mateoherrera-dev/paleta-pingpong/herramientas/segmentar.py

"""Segmenta los archivos crudos en ventanas individuales para Edge Impulse.

Uso:
    python herramientas/segmentar.py
"""
import pandas as pd
import pathlib

def main():
    crudos_dir = pathlib.Path("datos/crudos")
    salida_dir = pathlib.Path("datos/segmentados")
    
    if not crudos_dir.exists():
        print(f"No existe la carpeta {crudos_dir}. Asegurate de grabar datos primero.")
        return

    salida_dir.mkdir(parents=True, exist_ok=True)

    # Parámetros de la ventana (1000 Hz): 120 ms antes, 76 ms después = 196 ms total.
    # Tiene que coincidir con lo que espera el modelo: ML_BUFFER_LONGITUD_ESPERADA / 6 ejes
    # en firmware/paleta/ml_inference.h (y con el buffer circular del firmware).
    VENTANA_PRE = 120
    VENTANA_POST = 76

    archivos = list(crudos_dir.glob("*.csv"))
    if not archivos:
        print(f"No hay archivos CSV en {crudos_dir}")
        return

    total_ventanas = 0

    for ruta_csv in archivos:
        df = pd.read_csv(ruta_csv)
        
        # Validación rápida para asegurarse de que sea un archivo de la placa
        if 'impacto' not in df.columns or 't_us' not in df.columns:
            continue

        indices_impacto = df.index[df['impacto'] == 1].tolist()
        if not indices_impacto:
            continue
            
        print(f"Procesando {ruta_csv.name} ({len(indices_impacto)} impactos encontrados)...")

        # Inferir la etiqueta a partir del nombre original
        # GOLPES permitidos según senal.py
        etiqueta = "desconocido"
        for golpe in ["topspin_derecha", "topspin_reves", "empuje_derecha", "empuje_reves"]:
            if golpe in ruta_csv.name:
                etiqueta = golpe
                break

        for i, idx in enumerate(indices_impacto):
            inicio = idx - VENTANA_PRE
            fin = idx + VENTANA_POST
            
            # Si el impacto está muy cerca del borde del archivo, lo descartamos
            if inicio < 0 or fin > len(df):
                continue
                
            ventana = df.iloc[inicio:fin].copy()
            
            # Reindexar el timestamp para que arranque en 0 ms
            ventana['timestamp'] = ((ventana['t_us'] - ventana['t_us'].iloc[0]) / 1000).astype(int)
            
            # Exportar manteniendo los nombres de columnas originales del proyecto
            columnas_exportar = ['timestamp', 'ax_g', 'ay_g', 'az_g', 'gx_dps', 'gy_dps', 'gz_dps']
            ventana_limpia = ventana[columnas_exportar]
            
            # Formato de nombre especial para Edge Impulse: "etiqueta.identificador.csv"
            # Esto permite que Edge Impulse infiera la etiqueta "topspin_derecha" automáticamente.
            nombre_archivo = salida_dir / f"{etiqueta}.{ruta_csv.stem}_impacto_{i+1}.csv"
            
            ventana_limpia.to_csv(nombre_archivo, index=False)
            total_ventanas += 1

    print(f"\n¡Listo! Se generaron {total_ventanas} ventanas en '{salida_dir}'.")
    print("Podés subir esta carpeta directamente a Edge Impulse.")

if __name__ == "__main__":
    main()
